beargun/Trinky/pictures/trinky-99.png

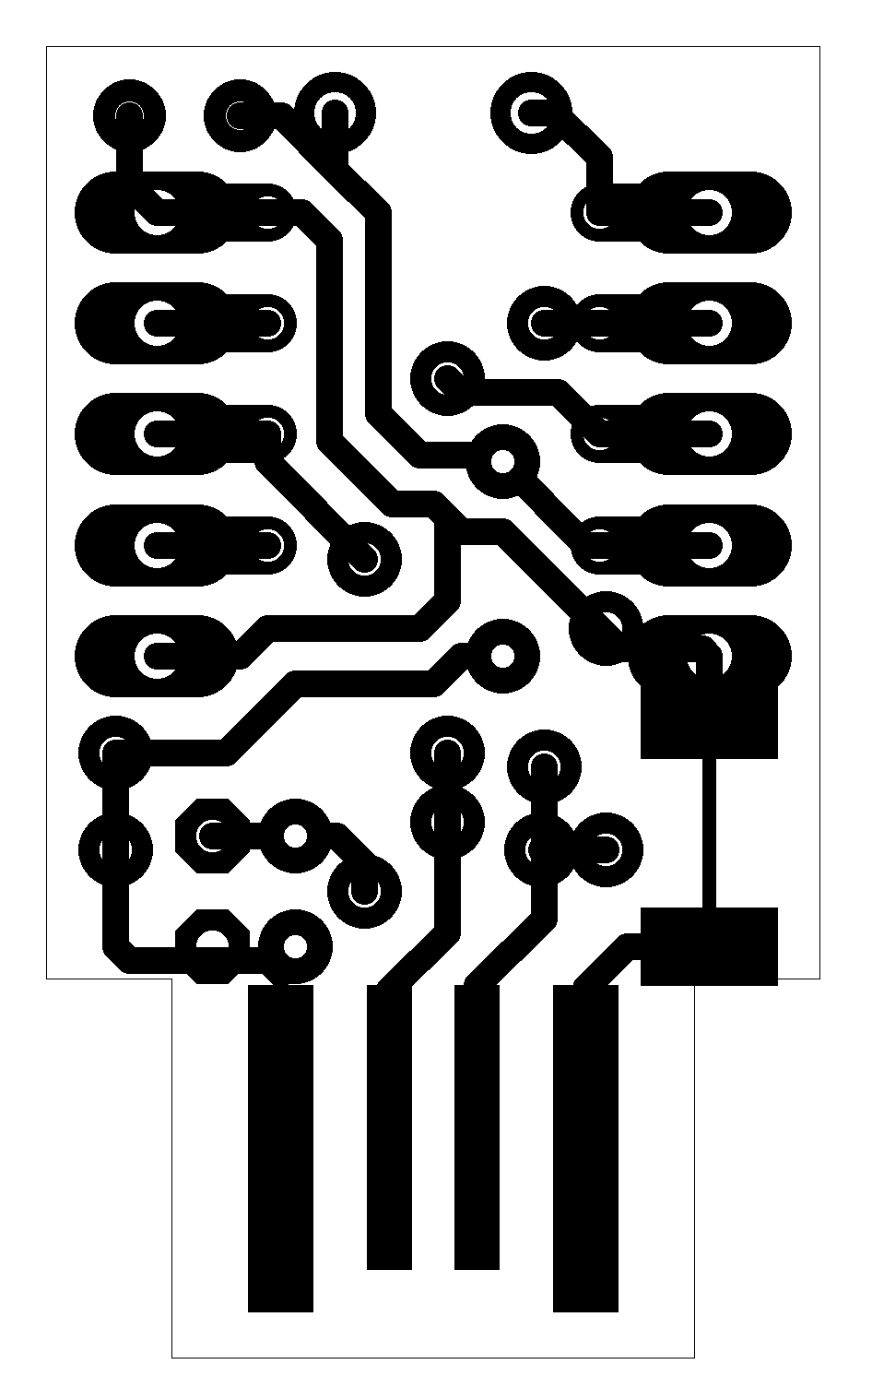
pictures/trinky-99.png
